todbot/pico8enc/docs/pico8enc_topshot_wh.png

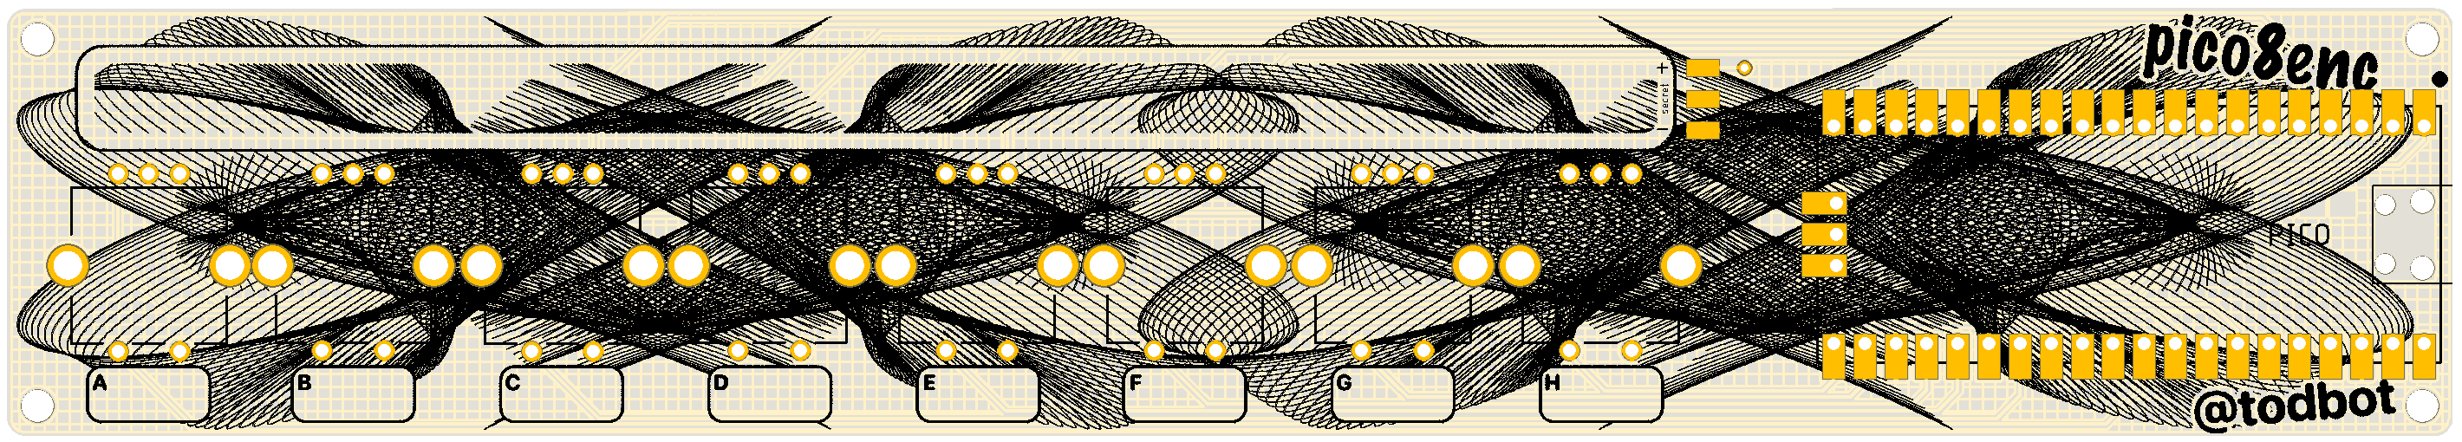
docs/pico8enc_topshot_wh.png
